Santos-Rui/mriscoc-custom/STL's/Klemco Holder/suport fang lateral v7.stl

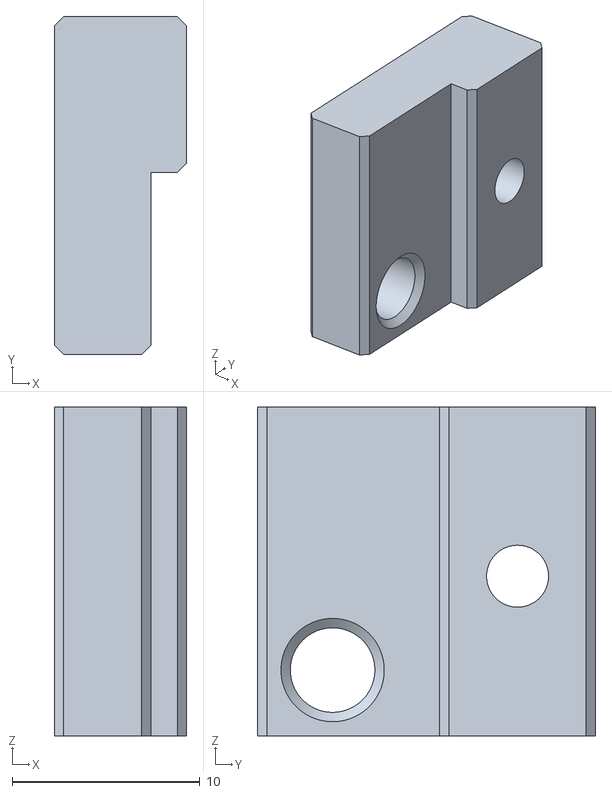
[picture p18: CAD file, 2023-04-12]
STL's/Klemco Holder/suport fang lateral v7.stl
7.05 x 18.0 x 17.5
