Santos-Rui/mriscoc-custom/STL's/Linear Rails/X Axis/Ad_X_endstop_side v2.stl

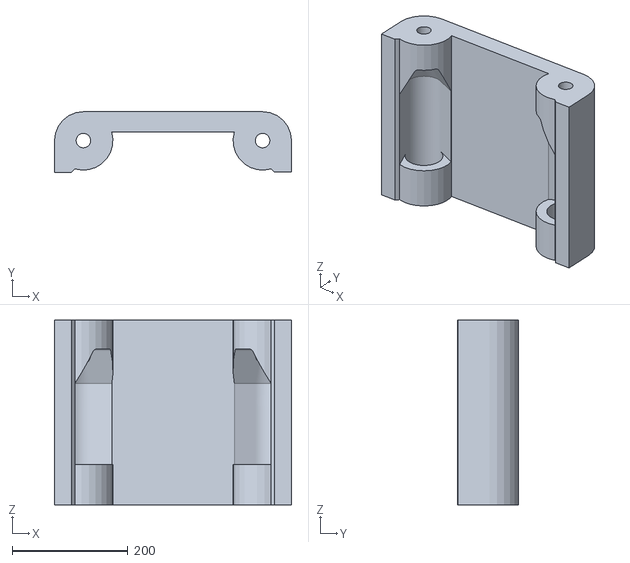
[picture p19: CAD file, 2023-04-12]
STL's/Linear Rails/X Axis/Ad_X_endstop_side v2.stl
410.0 x 104.9 x 320.0
