Santos-Rui/mriscoc-custom/STL's/Linear Rails/Y Axis/Y Rail Final EndStop v3.stl

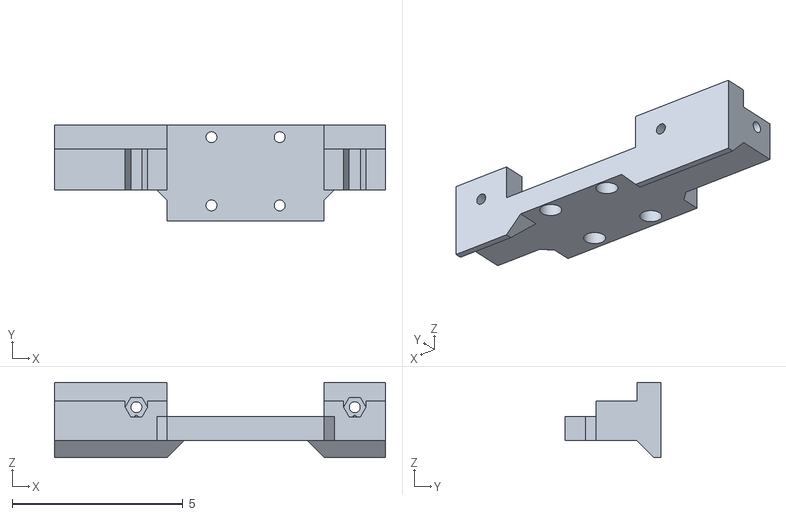
[picture p20: CAD file, 2023-04-19]
STL's/Linear Rails/Y Axis/Y Rail Final EndStop v3.stl
9.70 x 2.80 x 2.20
