Santos-Rui/mriscoc-custom/STL's/Linear Rails/Z Axis/Bottom Rail.stl

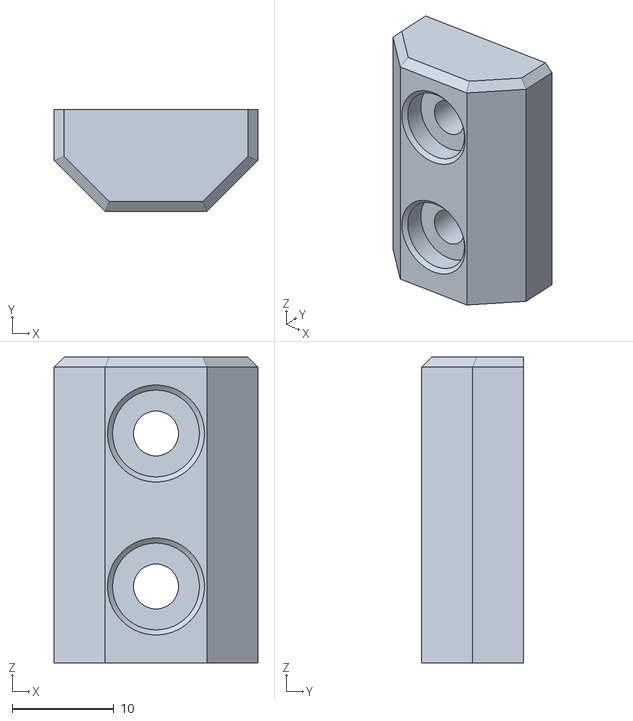
[picture p21: CAD file, 2023-04-10]
STL's/Linear Rails/Z Axis/Bottom Rail.stl
20.0 x 10.0 x 30.0
