Santos-Rui/mriscoc-custom/STL's/Noctuas Under/Ender_3_V2_PSU_Cover v1.stl

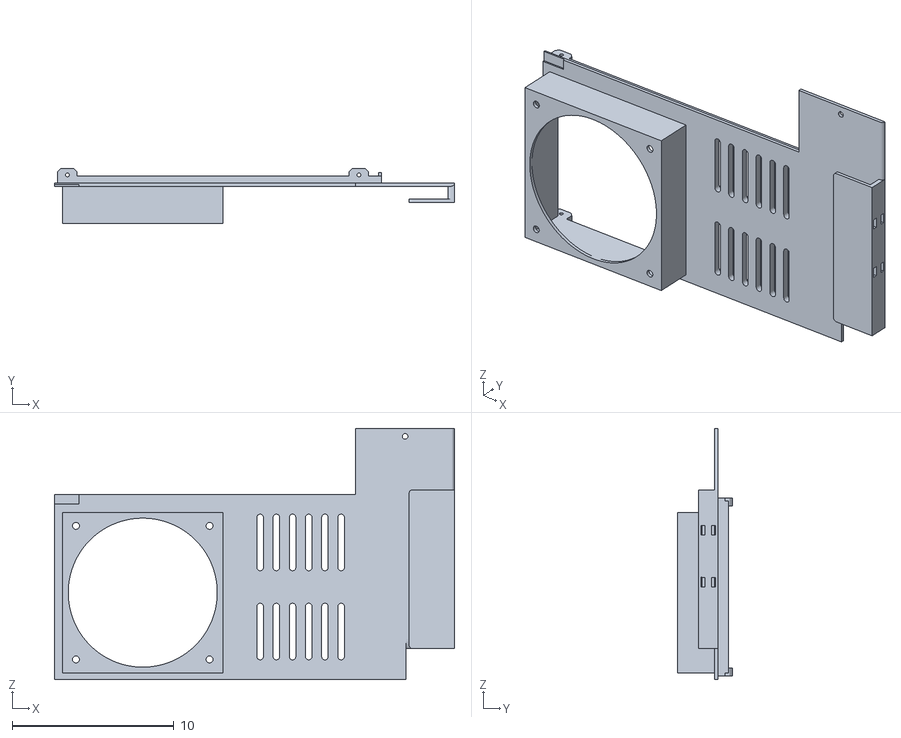
[picture p22: CAD file, 2023-04-12]
STL's/Noctuas Under/Ender_3_V2_PSU_Cover v1.stl
24.7 x 3.40 x 15.5
