Santos-Rui/mriscoc-custom/STL's/Cable Chains/hotend-mount v5.stl

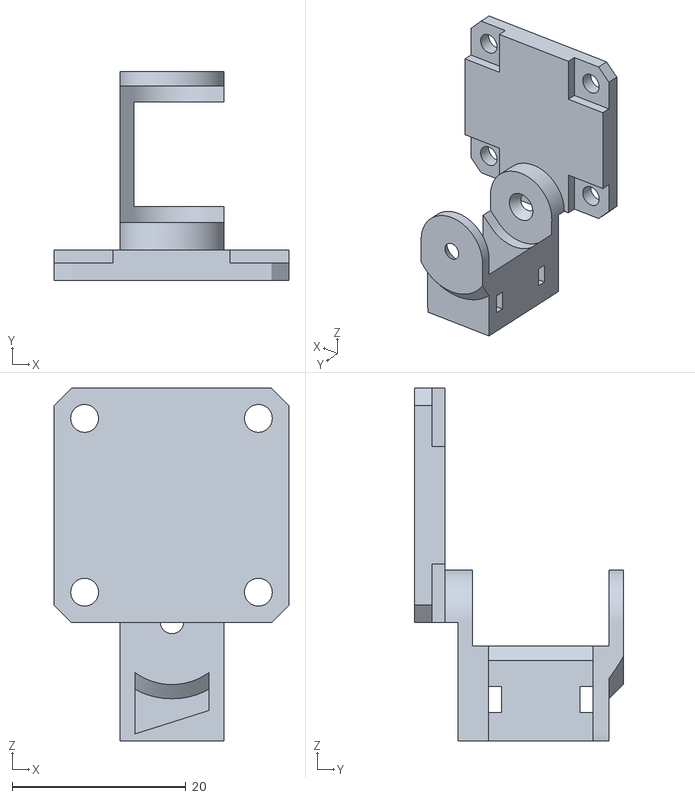
[picture p23: CAD file, 2023-04-12]
STL's/Cable Chains/hotend-mount v5.stl
27.0 x 24.0 x 40.6
