Santos-Rui/mriscoc-custom/STL's/Linear Rails/Y Axis/mount_adaptor_5mm.STL

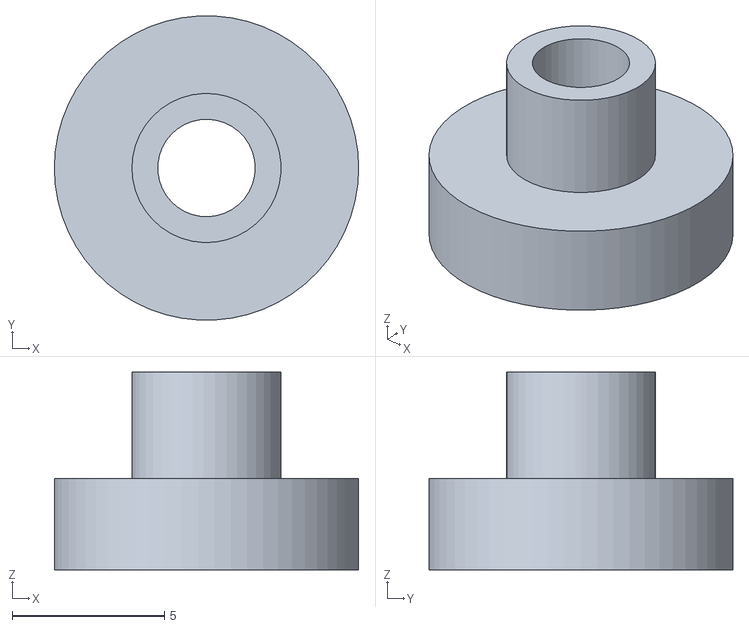
[picture p25: CAD file, 2023-04-10]
STL's/Linear Rails/Y Axis/mount_adaptor_5mm.STL
10.0 x 9.99 x 6.50
