Santos-Rui/mriscoc-custom/STL's/Linear Rails/Z Axis/Z column v1.stl

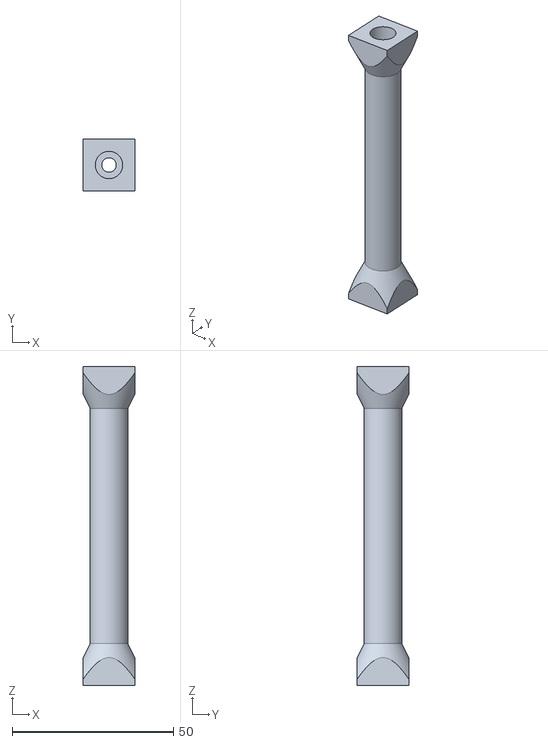
[picture p26: CAD file, 2023-04-10]
STL's/Linear Rails/Z Axis/Z column v1.stl
16.0 x 16.0 x 99.0
