Santos-Rui/mriscoc-custom/STL's/Cable Chains/slim-link.stl

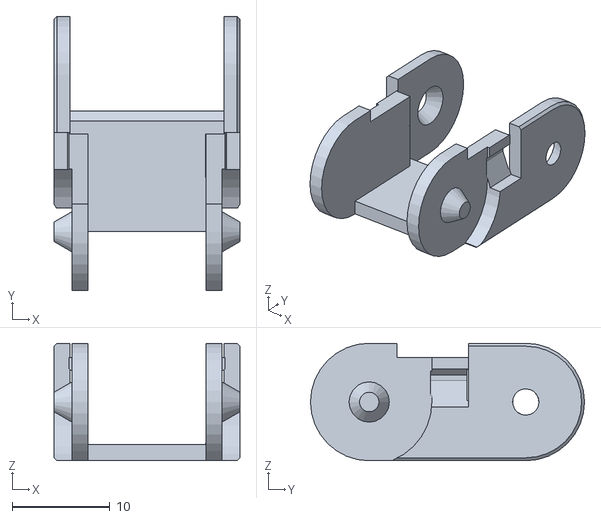
[picture p27: CAD file, 2023-04-12]
STL's/Cable Chains/slim-link.stl
19.0 x 28.0 x 12.0
