Santos-Rui/mriscoc-custom/STL's/Linear Rails/Y Axis/mount_adaptor_7mm.STL

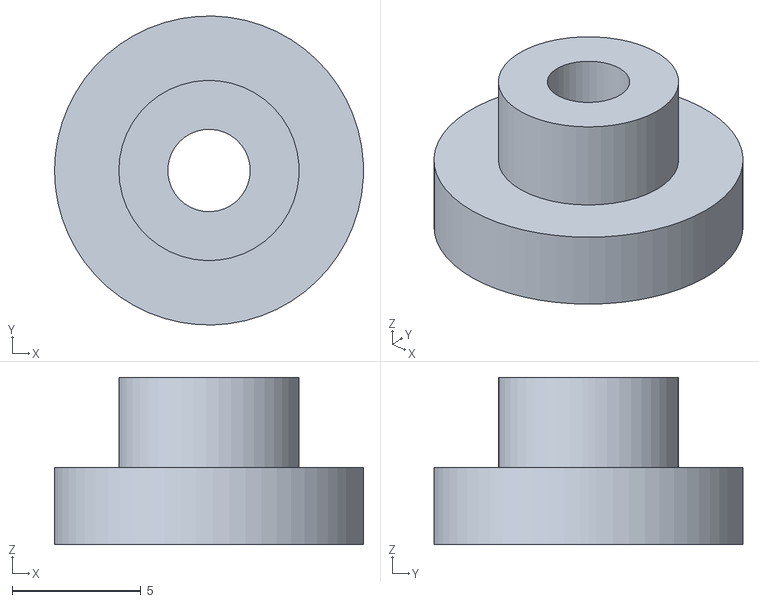
[picture p28: CAD file, 2023-04-10]
STL's/Linear Rails/Y Axis/mount_adaptor_7mm.STL
12.0 x 12.0 x 6.50
