Santos-Rui/mriscoc-custom/STL's/Cable Chains/cableChain_bedCorner_v2 custom v1.stl

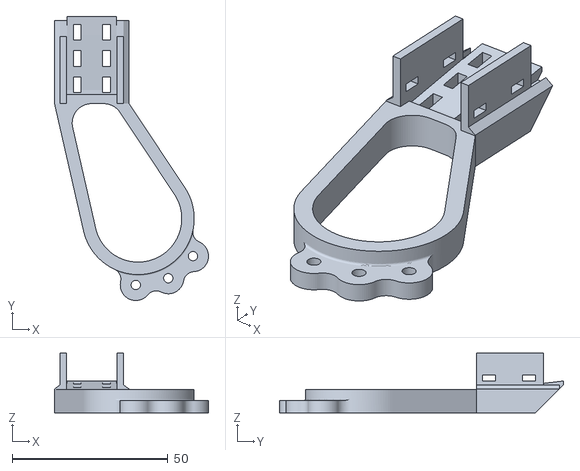
[picture p29: CAD file, 2023-04-12]
STL's/Cable Chains/cableChain_bedCorner_v2 custom v1.stl
49.5 x 91.3 x 19.2
