Santos-Rui/mriscoc-custom/STL's/Cable Chains/Not sure wich/extruder-mount-28mm-alu-dd.stl

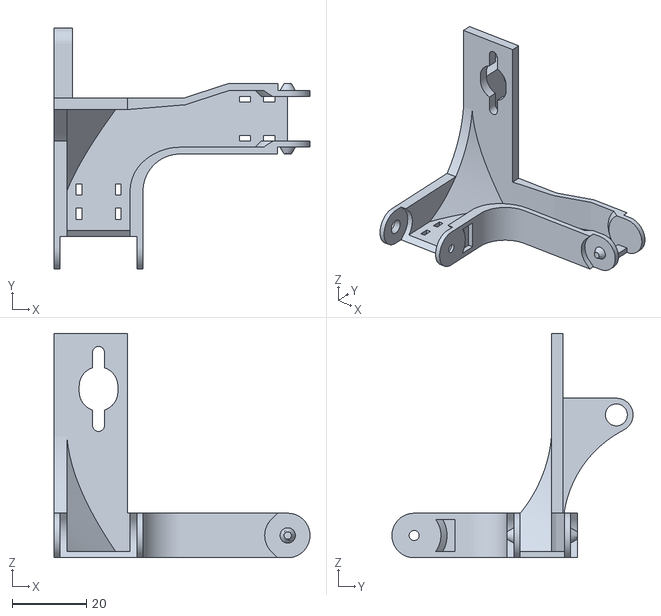
[picture p30: CAD file, 2023-04-12]
STL's/Cable Chains/Not sure wich/extruder-mount-28mm-alu-dd.stl
69.0 x 65.0 x 60.5
