Santos-Rui/mriscoc-custom/STL's/Linear Rails/Y Axis/rail_mount_guide.STL

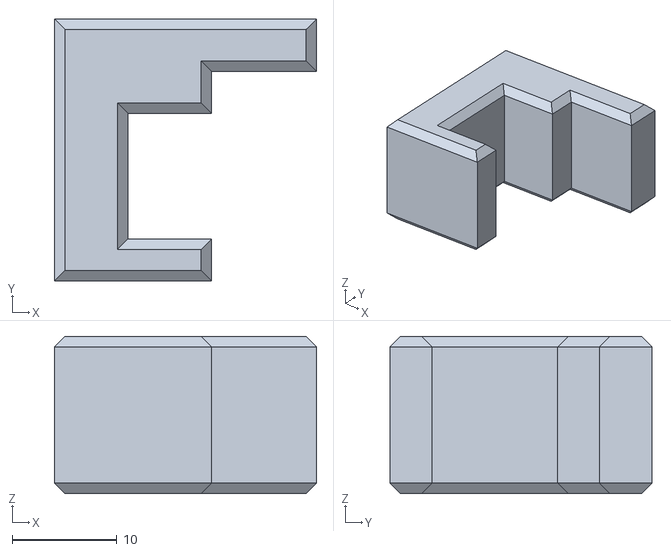
[picture p31: CAD file, 2023-04-10]
STL's/Linear Rails/Y Axis/rail_mount_guide.STL
25.0 x 25.0 x 15.0
