Santos-Rui/mriscoc-custom/STL's/Cable Chains/Not sure wich/extruder-mount-31mm-alu.stl

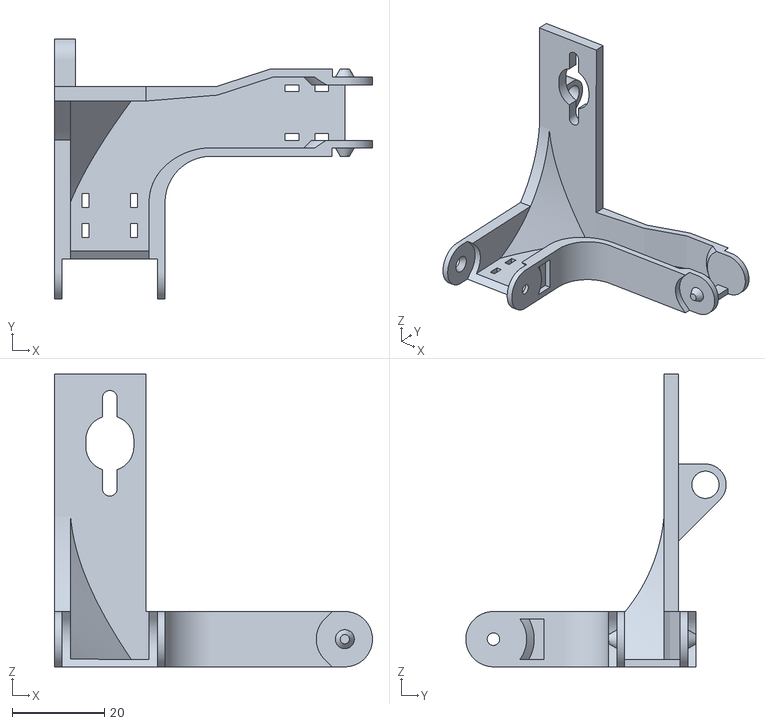
[picture p32: CAD file, 2023-04-12]
STL's/Cable Chains/Not sure wich/extruder-mount-31mm-alu.stl
69.0 x 56.5 x 63.5
