Santos-Rui/mriscoc-custom/STL's/Cable Chains/Not sure wich/extruder-mount-32mm-stock.stl

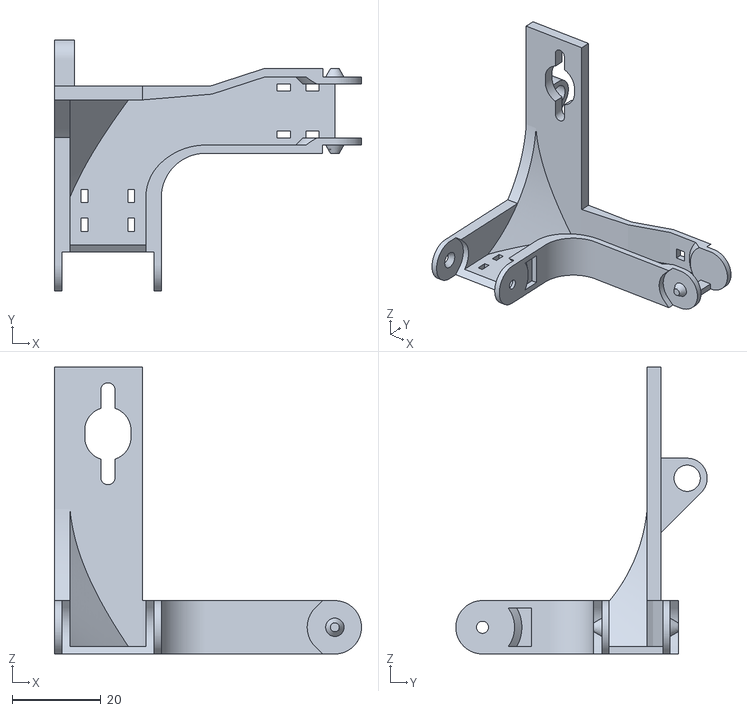
[picture p33: CAD file, 2023-04-12]
STL's/Cable Chains/Not sure wich/extruder-mount-32mm-stock.stl
69.0 x 56.5 x 64.5
