Santos-Rui/mriscoc-custom/STL's/Cable Chains/Not sure wich/extruder-mount-29mm-alu-dd.stl

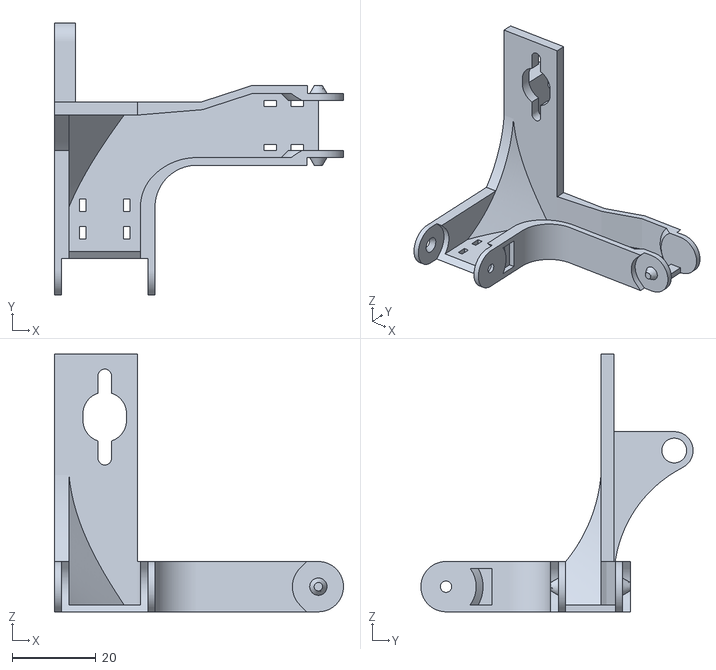
[picture p35: CAD file, 2023-04-12]
STL's/Cable Chains/Not sure wich/extruder-mount-29mm-alu-dd.stl
69.0 x 65.0 x 61.5
