Santos-Rui/mriscoc-custom/STL's/Cable Chains/Not sure wich/extruder-mount-30mm-alu-dd.stl

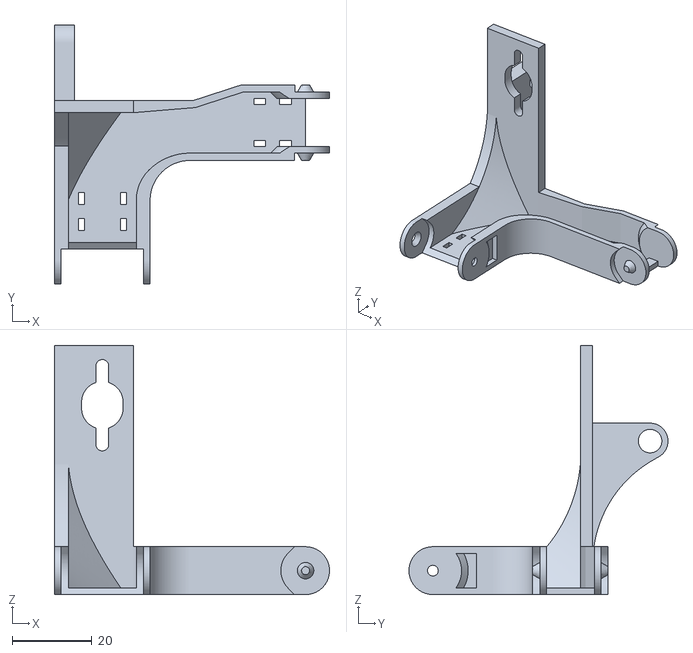
[picture p36: CAD file, 2023-04-12]
STL's/Cable Chains/Not sure wich/extruder-mount-30mm-alu-dd.stl
69.0 x 65.0 x 62.5
