Santos-Rui/mriscoc-custom/STL's/Cable Chains/Not sure wich/extruder-mount-32mm-alu-dd.stl

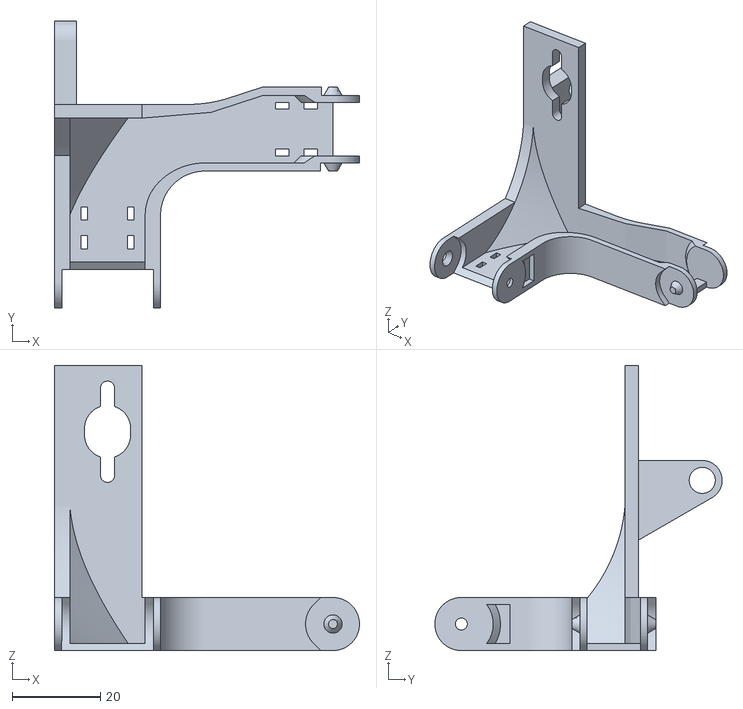
[picture p37: CAD file, 2023-04-12]
STL's/Cable Chains/Not sure wich/extruder-mount-32mm-alu-dd.stl
69.0 x 65.0 x 64.5
