Santos-Rui/mriscoc-custom/STL's/Cable Chains/Not sure wich/extruder-mount-30mm-alu.stl

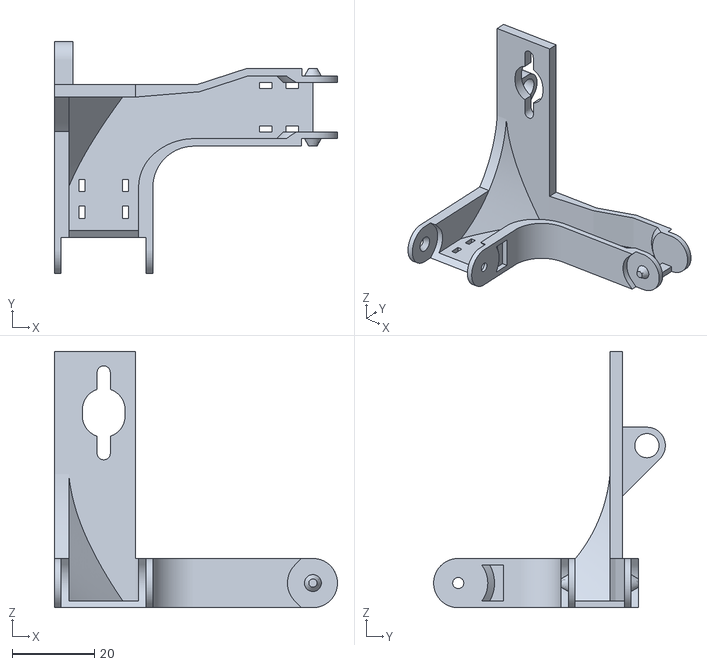
[picture p38: CAD file, 2023-04-12]
STL's/Cable Chains/Not sure wich/extruder-mount-30mm-alu.stl
69.0 x 56.5 x 62.5
